JohnDHitti/balancing-robot/images/board.JPG

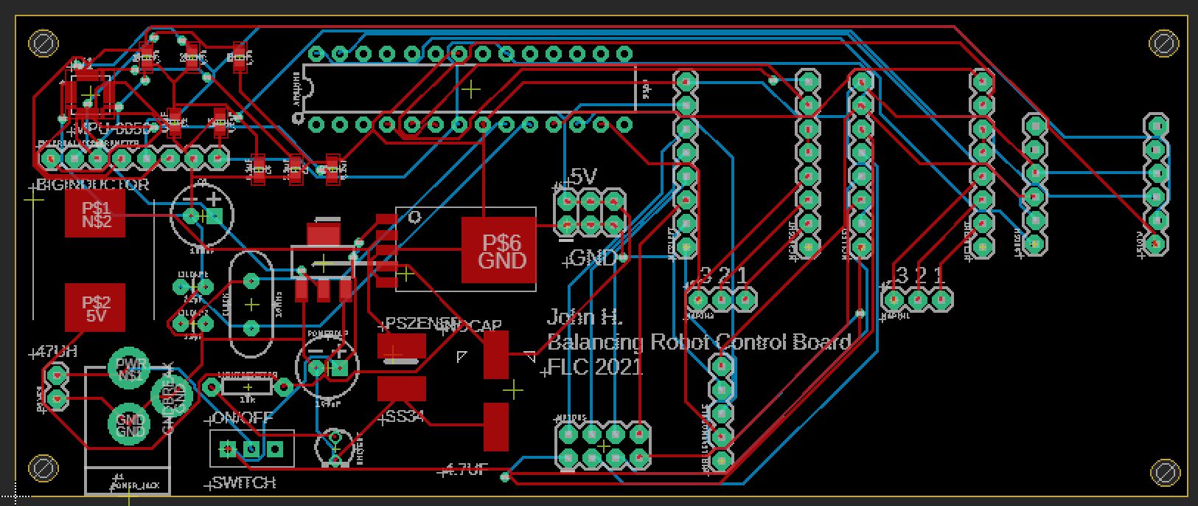
images/board.JPG
