JohnDHitti/balancing-robot/images/IMG_20211213_161746.jpg

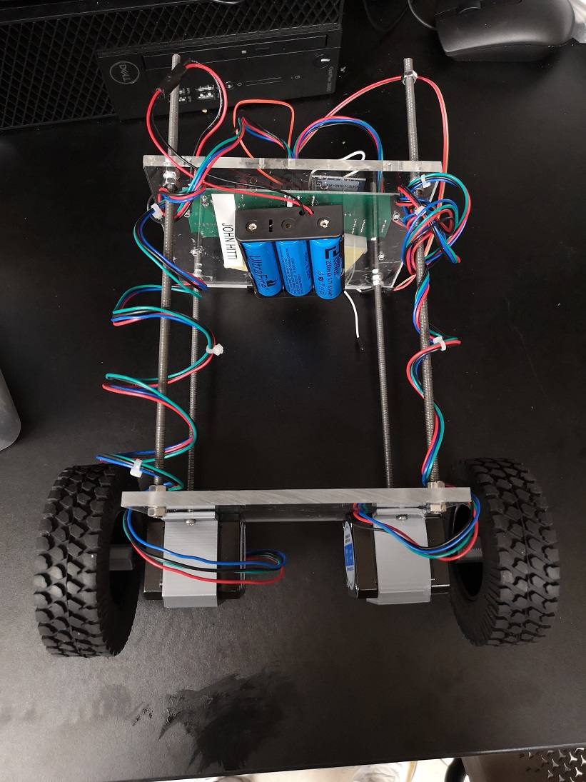
images/IMG_20211213_161746.jpg
