JohnDHitti/balancing-robot/images/IMG_20211213_161749.jpg

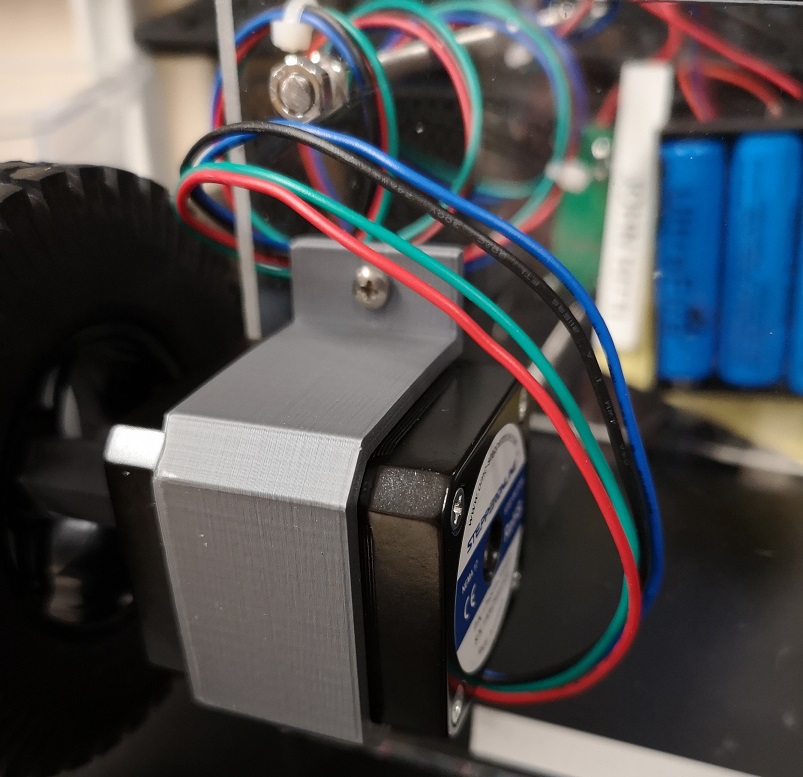
images/IMG_20211213_161749.jpg
