JohnDHitti/balancing-robot/images/IMG_20211213_161816.jpg

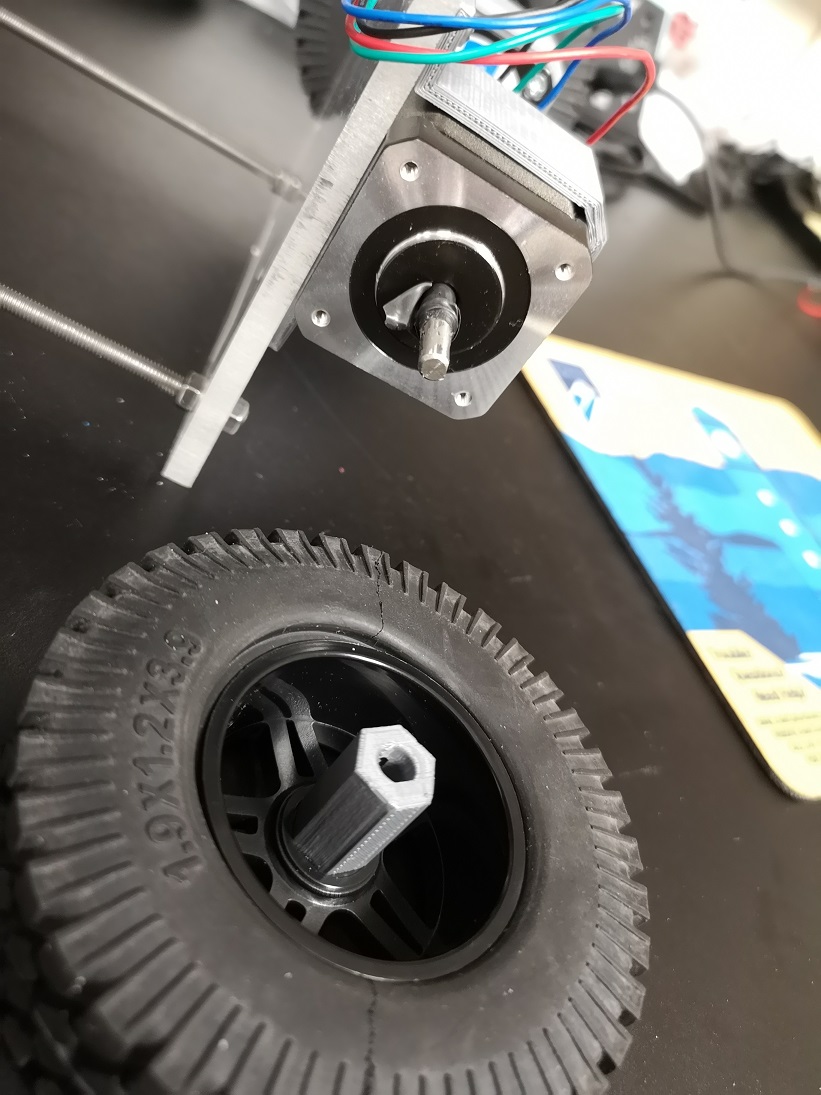
images/IMG_20211213_161816.jpg
