JohnDHitti/balancing-robot/images/js board.JPG

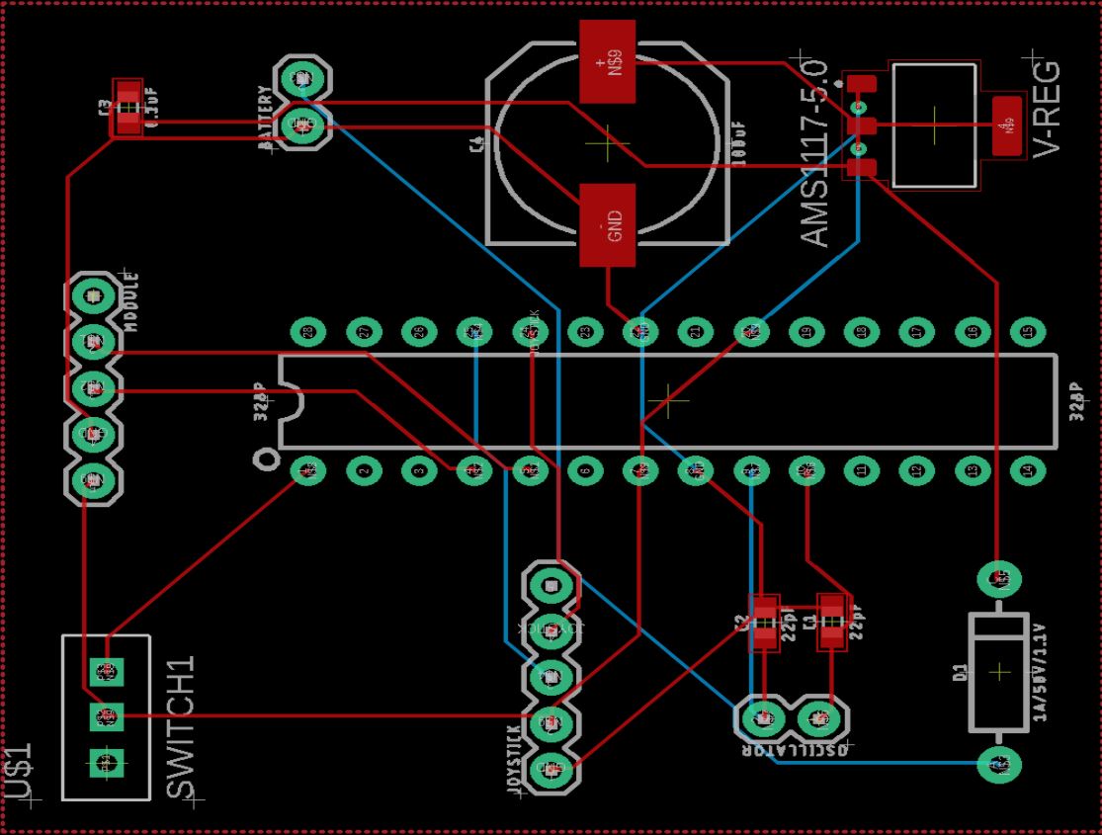
images/js board.JPG
